Impulse-Response/ECG-Signal-Acquisition-and-Data-Processing/Software/MATLAB-Core/img/power.png

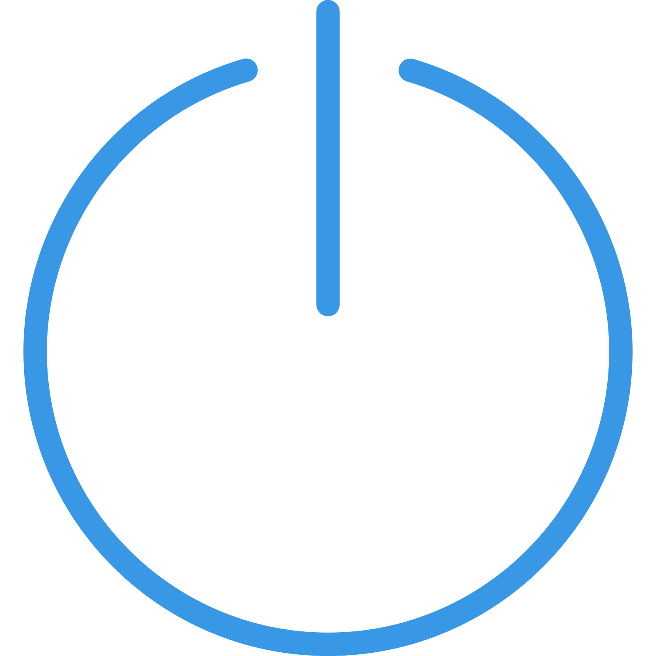
Software/MATLAB-Core/img/power.png
